sq6sfo/espBode/esp_network.h

#ifndef _ESP_NETWORK_H_
#define _ESP_NETWORK_H_

typedef struct
{
    uint32_t   frag;
    uint32_t   xid;
    uint32_t   msg_type;
    uint32_t   rpc_version;
    uint32_t   program;
    uint32_t   program_version;
    uint32_t   procedure;
    uint32_t   credentials_l;
    uint32_t   credentials_h;
    uint32_t   verifier_l;
    uint32_t   verifier_h;
}rpcreq_header;

typedef struct
{
    uint32_t   frag;
    uint32_t   xid;
    uint32_t   msg_type;
    uint32_t   reply_state;
    uint32_t   verifier_l;
    uint32_t   verifier_h;
    uint32_t   rpc_status;
}rpcresp_header;

typedef struct
{
    rpcreq_header  header;

    uint32_t   getport_program;
    uint32_t   getport_version;
    uint32_t   getport_protocol;
    uint32_t   getport_port;
}rpcreq_getport;

typedef struct
{
    rpcresp_header  header;

    uint32_t   vxi_port;
}rpcresp_getport;

typedef struct
{
    rpcreq_header   header;

    uint32_t   linkId;
    uint32_t   ioTimeout;
    uint32_t   lockTimeout;
    uint32_t   flags;
    uint32_t   dataLen;
    uint8_t    data[];

}rcpreq_devReadWrite;

typedef struct
{
    rpcresp_header   header;

    uint32_t   errorCode;
    uint32_t   reason;
    uint32_t   dataLen;
    uint8_t    data[];

}rcpresp_devReadWrite;

typedef struct
{
    rpcresp_header  header;

    uint32_t   errorCode;
    uint32_t   linkId;
    uint32_t   abortPort;
    uint32_t   maxReceiveSize;
}rpcresp_createLink;

uint8_t handlePacket(WiFiClient client);

#endif /* _ESP_NETWORK_H_ */
